michar71/midi_arm2/src/baboi_protocol.cpp

#include <arduino.h>
#include "baboi_protocol.h"
#include "baboi_sensors.h"
#include "baboi_led.h"
#include "settings.h"
#include "main.h"
#include <AsyncUDP.h>

AsyncUDP udp;
extern setup_t settings;

t_comm_channel currentCommChannel = COMM_SERIAL;
IPAddress comm_host_ip = IPAddress(0,0,0,0);
long lastPing = 0;


/*Combined use of Serial and Wifi
//-------------------------------

- Baboi listens both on Serial and Wifi on itintation of contact via 'Q' command
- If a serial command is received all engotiation happens via Serial
- If a Q command is received the 'I' Command will be send as a broadcast command
- Following D commands are send as a Unicast command to the adress of the host where the Q command originated from
*/ 


char send_data[SEND_DATA_LENGTH];
char receive_data[RECEIVE_DATA_LENGTH];

extern t_state state;
extern bool but_a_state;
extern bool but_b_state;
extern bool but_c_state;

extern String devicename;
extern int maj_ver;
extern int min_ver;

//Build Data string to send.
//Indivudal fields are seperated by ':'
//Format for Controller Data (C) commands is
//Command ID 'C'
//Device Name 'BABOI'
//Device FW Major
//Device FW Minor
//Device HW Version
//Unique Device ID (0..255), 0 = Single, 1 = left, 2 = right



void build_processing_data(bool senddata)
{
  float yaw_val = 0;
  float pitch_val = 0;
  float roll_val = 0;
  float ax_val = 0;
  float ay_val = 0;
  float az_val = 0;

  if (checkForMCU())
  {
    yaw_val = mpu_GetCurrentYaw();
    pitch_val = mpu_GetCurrentPitch();
    roll_val = mpu_GetCurrentRoll();  
    ax_val = mpu_GetCurrentAX();
    ay_val = mpu_GetCurrentAY();  
    az_val = mpu_GetCurrentAZ();
  }

  int16_t tension_ch1 = -1;
  int16_t tension_ch2 = -1;


  if (checkForGlove())
  {
    tension_ch1 = tension_get_ch(0);
    tension_ch2 = tension_get_ch(1);   
  }

  if(senddata)
    snprintf(send_data,SEND_DATA_LENGTH,"%c:%.2f:%.2f:%.2f:%.2f:%.2f:%.2f:%d:%d",ID_DATA,yaw_val,pitch_val,roll_val,ax_val,ay_val,az_val,tension_ch1,tension_ch2);
  else
    snprintf(send_data,SEND_DATA_LENGTH,"%c:0:0:0:0:0:0:0:0",ID_DATA);

    //#TODO Combine into one bitmap
    if (state == STATE_LIVE)
      strcat(send_data,":1");
    else
      strcat(send_data,":0");

    if (but_a_state)
      strcat(send_data,":1");
    else
      strcat(send_data,":0");

    //Button B/C not used
      strcat(send_data,":0");        
      strcat(send_data,":0");   
}

void send_processing_data(bool senddata)
{
  build_processing_data(senddata);
  if (currentCommChannel == COMM_SERIAL)
  {  
    Serial.println(send_data);  
  }
  else
  {
    AsyncUDPMessage message;
    message.printf("%s",send_data);

    //Sending everything as broadcast right now. Replace with unicast later    
    //udp.broadcastTo(message, UDP_BROADCAST_PORT);
    udp.sendTo(message, comm_host_ip, UDP_BROADCAST_PORT);
  }
}

void build_info_data(void)
{
  snprintf(send_data,SEND_DATA_LENGTH,"%c:%s:%d:%d:%d:%d",ID_INFO,devicename,maj_ver,min_ver,BABOI_HW_VER,settings.pos);
}

void send_info_data(void)
{
  build_info_data();  
  if (currentCommChannel == COMM_SERIAL)
  {  
        Serial.flush();
        Serial.println(send_data);
  }
  else
  {
      AsyncUDPMessage message;
      message.printf("%s",send_data);    
      udp.broadcastTo(message, UDP_BROADCAST_PORT);
  }

}

// Function to parse a comma-separated string into integers
int parseCSV(char *input, uint8_t *values, int maxValues) 
{
  char *token = strtok(input, ",");
  int count = 0;
  
  while (token != NULL && count < maxValues) 
  {
    values[count++] = (uint8_t)atoi(token); // Convert token to integer and store it
    token = strtok(NULL, ",");
  }
  
  return count; // Return the number of values parsed
}

void parse_LED_data(void)
{
  uint8_t data[16*3];
  uint8_t res = parseCSV(&receive_data[2], data, 16*3);
  if (res == 16*3)
  {
    SetLEDsFromArray(data);
  }
}


bool process_incoming_data(t_comm_channel commChannel)
{
    if (receive_data[0] == ID_QUERY)
    {
      //Set the comm channel active we got the message on
      currentCommChannel = commChannel;
      //Send back info data on comm channel
      send_info_data();
      return true;
    }
    else if (receive_data[0] == ID_REQUEST)
    {
      //Mark State as connected
      setState(STATE_LIVE);
      lastPing = millis();
      return true;
    }

    else if (receive_data[0] == ID_SETUP)
    {
      if (receive_data[2] == '0')
      {
        setState(STATE_CAL_GYRO);
      }
      else if (receive_data[2] == '1')
      {
        setState(STATE_CAL_TENSION);
      }
      else
      {

      }
      return true;
    }
    else if (receive_data[0] == ID_PING)
    {
      lastPing = millis();
      return true;
    }
   else if (receive_data[0] == ID_LED)
    {
      lastPing = millis(); //LED Data aslso acts as ping...
      parse_LED_data();
      return true;
    }    
    return false;
}

void incoming_protocol_request(void)
{
  static uint8_t len = 0;  
  char incomingByte;
  static bool complete = false;

  while (Serial.available() > 0) 
  {
    // read the incoming byte:
    incomingByte = Serial.read();
    receive_data[len++] = incomingByte;

    //resetting
    if (len == RECEIVE_DATA_LENGTH-2) 
    {
      len = 0;
      complete = false;
      receive_data[RECEIVE_DATA_LENGTH-1] = 0;
    }

    if (incomingByte == '\n')
    {
        complete = true;   
        receive_data[len++] = 0;
    }

    if (complete)
    {
        
        if (process_incoming_data(COMM_SERIAL))
          toggle_status_led();
        len = 0;
        complete = false;
        return;
    }
  } 
}


bool checkCommTimeout(void)
{
  const uint16_t timeout = 1200; //Longer then the 1 sec intervall on the host...
  if (millis() - lastPing > timeout)
    return true;
  else 
    return false;  
}


void setup_udp_broadcast_receiver()
{
    udp.onPacket([](AsyncUDPPacket packet) 
    {
      //if (packet.isBroadcast())
      {
        int ii=0;
        //Well... The packet made it here.. lets try to parse it
        uint8_t *pdata = packet.data();

        if (packet.length()< RECEIVE_DATA_LENGTH-1)
        {
            for (ii=0;ii<packet.length();ii++)
                receive_data[ii] = (char)pdata[ii];

            //Only store adress and use it if its a packet for us
            if (true == process_incoming_data(COMM_WIFI))
                comm_host_ip = packet.remoteIP();
        }
      }
        
    /*
      //Debug only
      Serial.print("UDP Packet Type: ");
      Serial.print(packet.isBroadcast()?"Broadcast":packet.isMulticast()?"Multicast":"Unicast");
      Serial.print(", From: ");
      Serial.print(packet.remoteIP());
      Serial.print(":");
      Serial.print(packet.remotePort());
      Serial.print(", To: ");
      Serial.print(packet.localIP());
      Serial.print(":");
      Serial.print(packet.localPort());
      Serial.print(", Length: ");
      Serial.print(packet.length());
      Serial.print(", Data: ");
      Serial.write(packet.data(), packet.length());
      Serial.println();
    */
    
    });

    #ifdef DEBUG
    Serial.println("UDP Receiver started");
    #endif
}


void init_protocol(void)
{
    //This should be the Broadcast IP address
    if(udp.listen(UDP_BROADCAST_PORT)) 
    {
      setup_udp_broadcast_receiver();
    }
}
