michar71/midi_arm2/Processing/BAB01/littlehelpers/examples/UDPHelperExample/UDPHelperExample.pde

import com.bckmnn.udp.*;
import java.net.InetSocketAddress;
import java.net.InetAddress;
import java.net.SocketAddress;

UDPHelper udp;

void setup(){
  udp = new UDPHelper(this);
  udp.setLocalPort(13370);
  udp.startListening();
}

void draw(){
  
}

public void onUdpMessageRecieved(SocketAddress client, byte[] message){
  String messageString = UDPHelper.stringFromBytes(message);
  println(client + " sent you this message: " + messageString);
}

void keyPressed(){
  if(key == 'a'){
    try{
      SocketAddress all = new InetSocketAddress(InetAddress.getByName("255.255.255.255"),13370);
      udp.sendMessage(UDPHelper.bytesFromString("message to all"),all);
    } catch(Exception e){
      e.printStackTrace();
    }
  }else if(key == 'l'){
    try{
      SocketAddress all = new InetSocketAddress(InetAddress.getByName("127.0.0.1"),13370);
      udp.sendMessage(UDPHelper.bytesFromString("message to self"),all);
    } catch(Exception e){
      e.printStackTrace();
    }
  }
}
